ojg/thatmicpre/desktop/plots/thatmicpre_3dview.png

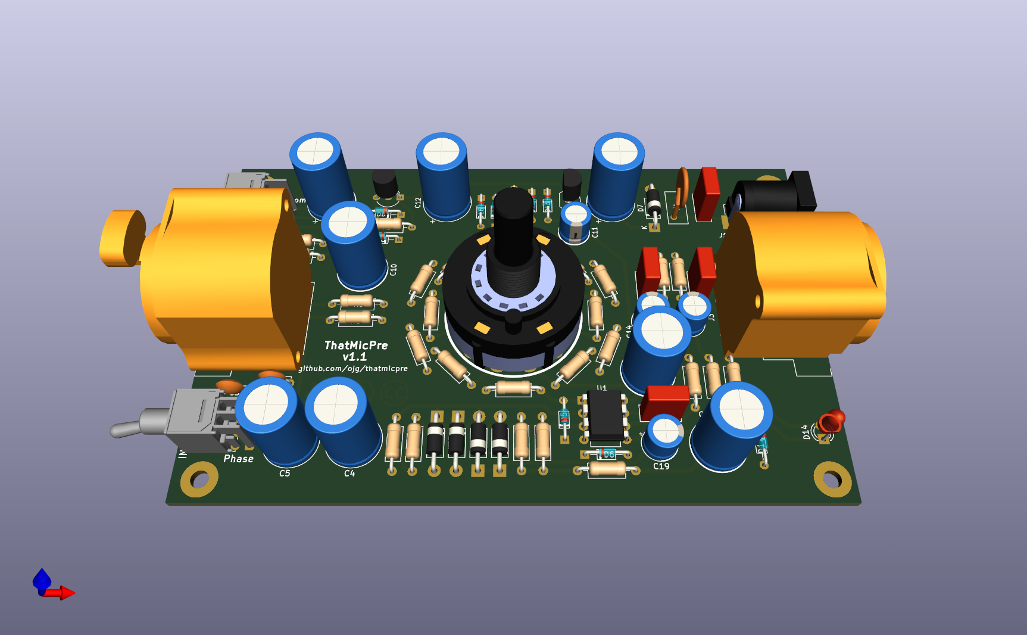
desktop/plots/thatmicpre_3dview.png
